andriibessarab/skewbot/cad/Vex Parts/Robot Battery (Li-Ion) (228-7045).SLDPRT

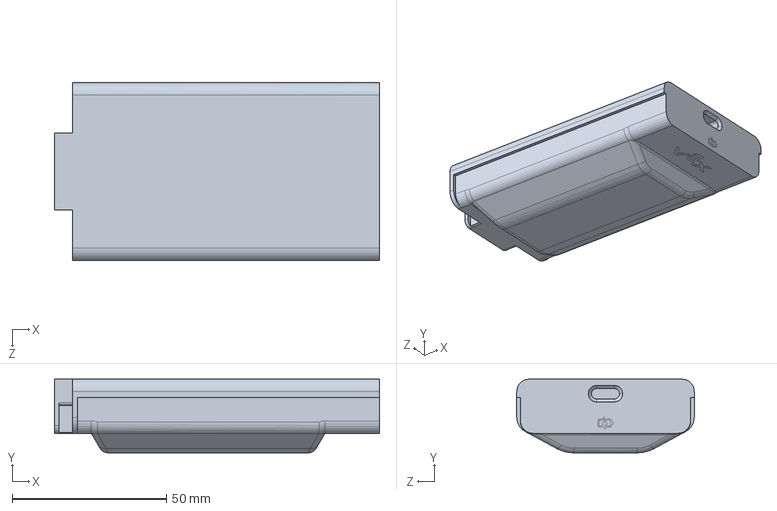
[picture p3: CAD file, 2025-11-20]
cad/Vex Parts/Robot Battery (Li-Ion) (228-7045).SLDPRT
105.5 x 23.9 x 57.6 mm
