andriibessarab/skewbot/cad/Vex Parts/2x Wide, 2x2 Corner Connector (228-2500-134).SLDPRT

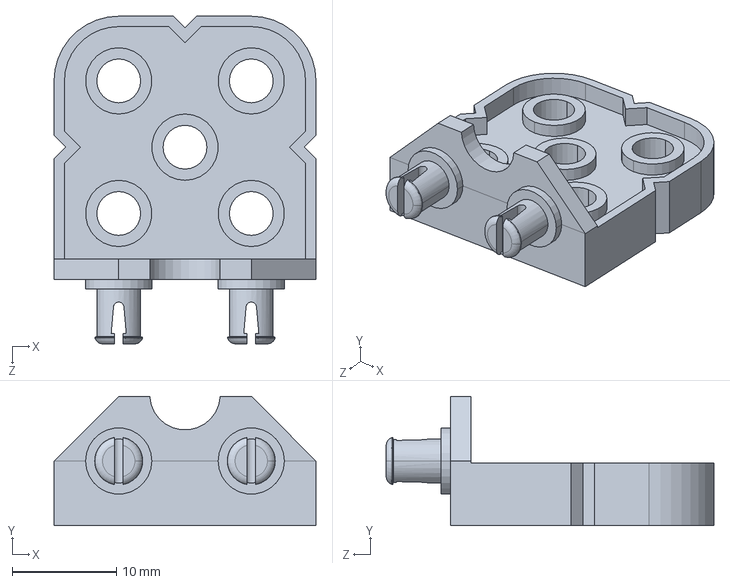
[picture p4: CAD file, 2025-11-20]
cad/Vex Parts/2x Wide, 2x2 Corner Connector (228-2500-134).SLDPRT
25.1 x 12.4 x 31.4 mm
