andriibessarab/skewbot/cad/Vex Parts/1x2 Connector Pin (228-2500-061).SLDPRT

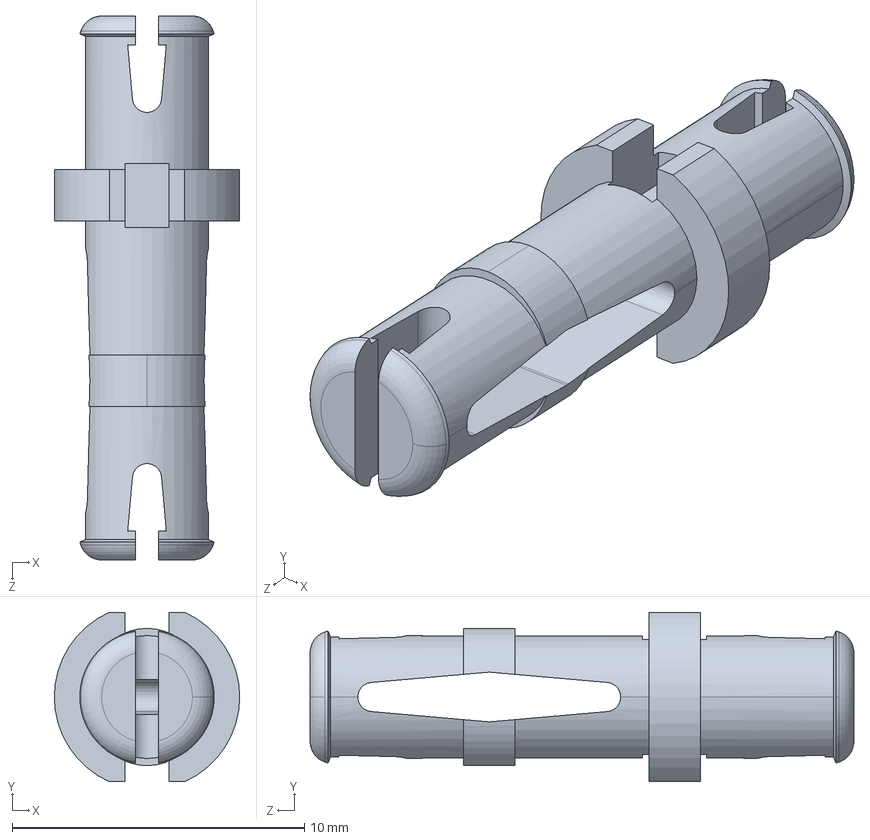
[picture p5: CAD file, 2025-11-20]
cad/Vex Parts/1x2 Connector Pin (228-2500-061).SLDPRT
6.35 x 5.80 x 18.6 mm
