andriibessarab/skewbot/cad/Vex Parts/VEX IQ Robot Brain Gen 2 (228-6480).SLDPRT

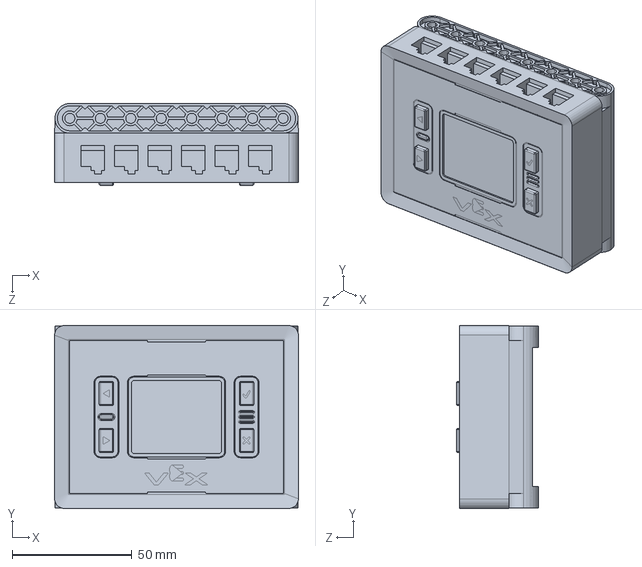
[picture p6: CAD file, 2025-11-20]
cad/Vex Parts/VEX IQ Robot Brain Gen 2 (228-6480).SLDPRT
101.7 x 76.3 x 34.2 mm
