andriibessarab/skewbot/cad/Vex Parts/1x4 Beam (228-2500-003).SLDPRT

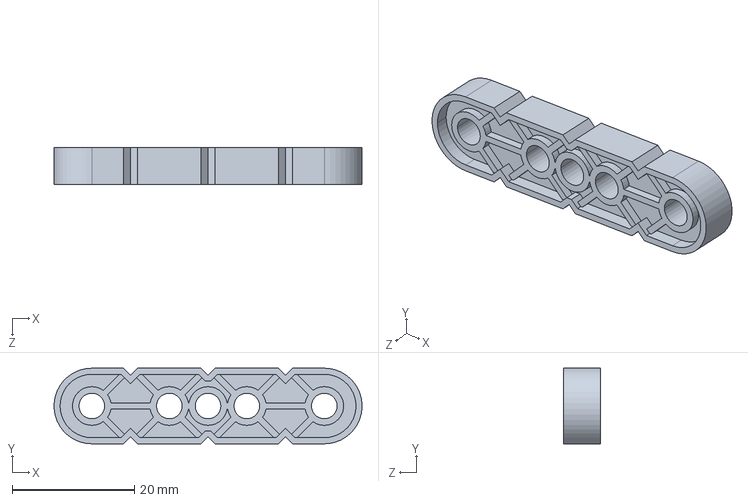
[picture p7: CAD file, 2025-11-20]
cad/Vex Parts/1x4 Beam (228-2500-003).SLDPRT
50.5 x 12.4 x 6.10 mm
