andriibessarab/skewbot/cad/Vex Parts/3x3 45 Degree Angle Beam (228-2500-148).SLDPRT

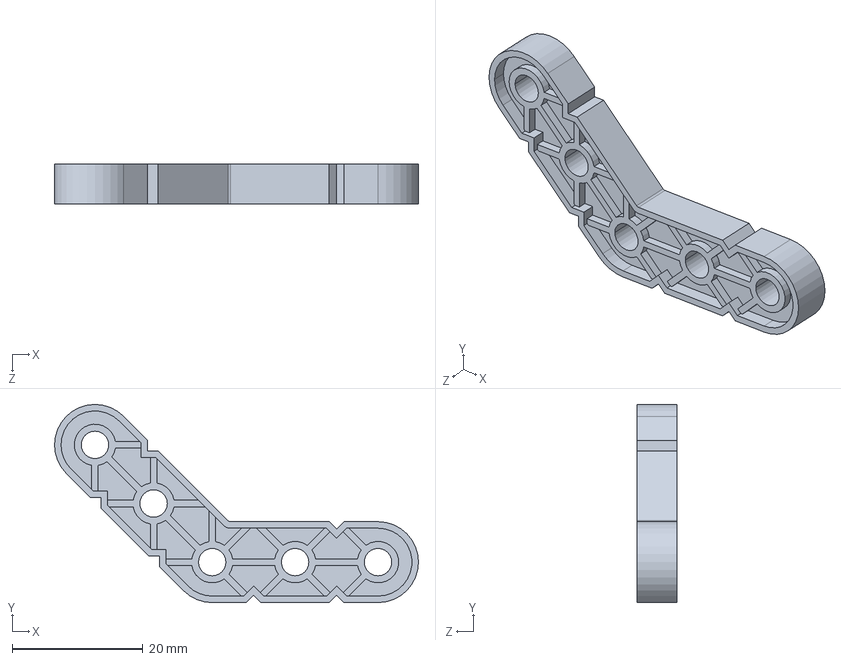
[picture p8: CAD file, 2025-11-20]
cad/Vex Parts/3x3 45 Degree Angle Beam (228-2500-148).SLDPRT
55.8 x 30.4 x 6.10 mm
