andriibessarab/skewbot/cad/Parts/Mirror Motor Mount Left.SLDPRT

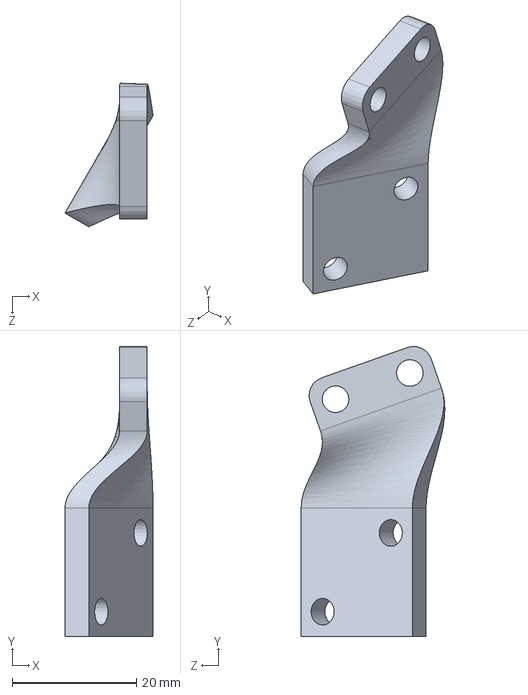
[picture p9: CAD file, 2025-11-20]
cad/Parts/Mirror Motor Mount Left.SLDPRT
14.2 x 46.8 x 23.2 mm
