andriibessarab/skewbot/cad/Vex Parts/1x3 Beam (228-2500-002).SLDPRT

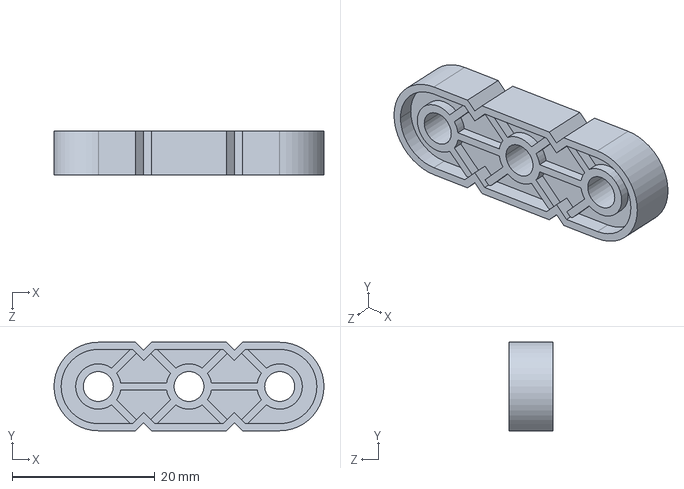
[picture p10: CAD file, 2025-11-20]
cad/Vex Parts/1x3 Beam (228-2500-002).SLDPRT
37.8 x 12.4 x 6.10 mm
