andriibessarab/skewbot/cad/Vex Parts/3x5 Right Angle Beam (228-2500-150).SLDPRT

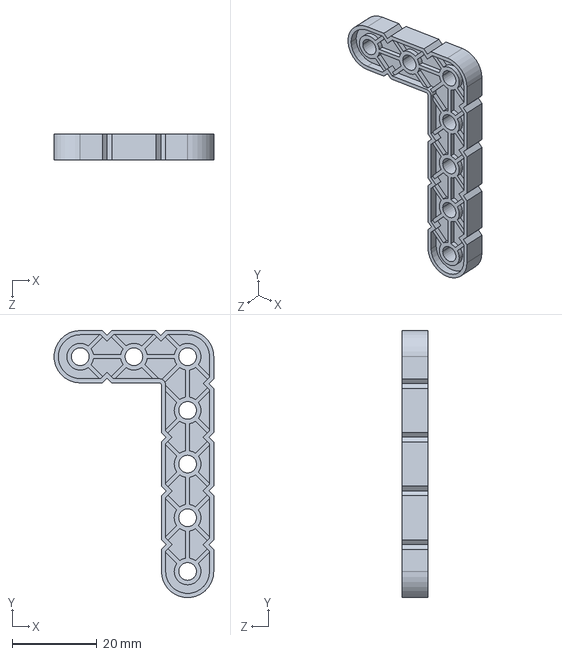
[picture p11: CAD file, 2025-11-20]
cad/Vex Parts/3x5 Right Angle Beam (228-2500-150).SLDPRT
37.8 x 63.2 x 6.10 mm
