andriibessarab/skewbot/cad/Parts/Top Back Brace.SLDPRT

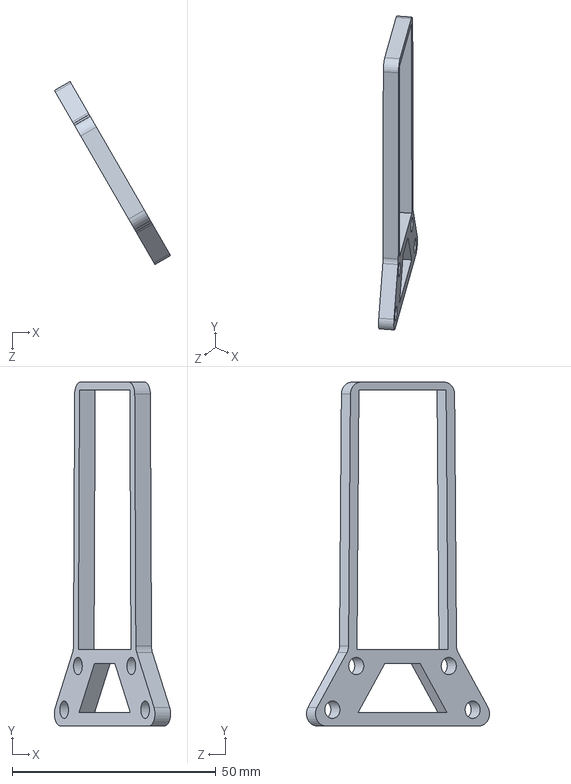
[picture p12: CAD file, 2025-11-20]
cad/Parts/Top Back Brace.SLDPRT
28.6 x 84.5 x 45.0 mm
