andriibessarab/skewbot/cad/Vex Parts/3x Motor Shaft.SLDPRT

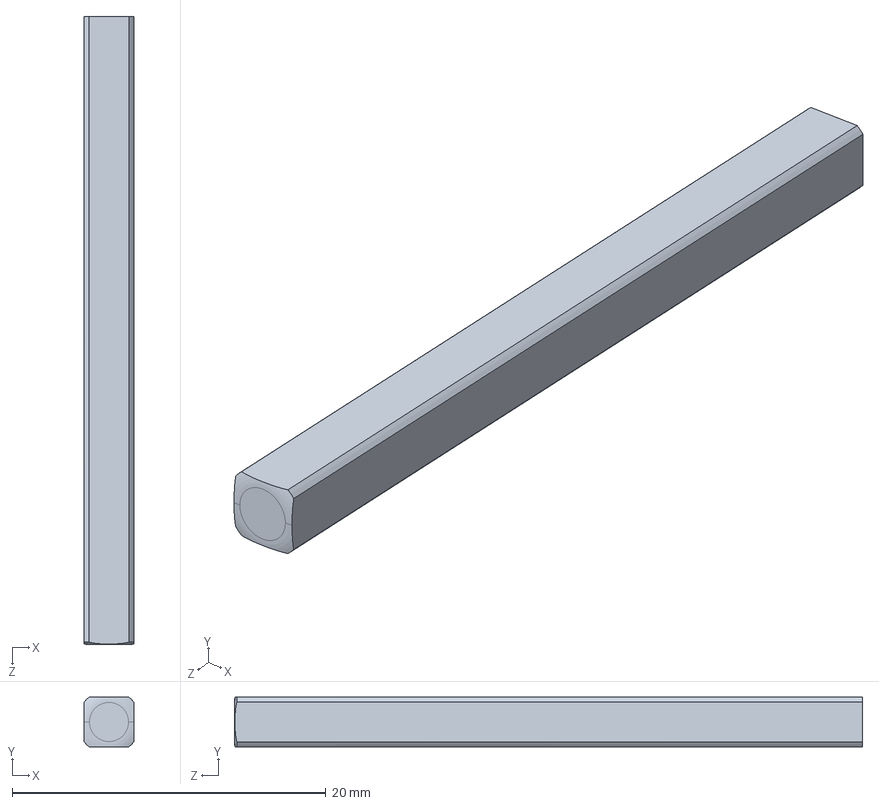
[picture p13: CAD file, 2025-11-20]
cad/Vex Parts/3x Motor Shaft.SLDPRT
3.17 x 3.17 x 40.0 mm
