andriibessarab/skewbot/cad/Vex Parts/VEX IQ Optical Sensor (228-7082).SLDPRT

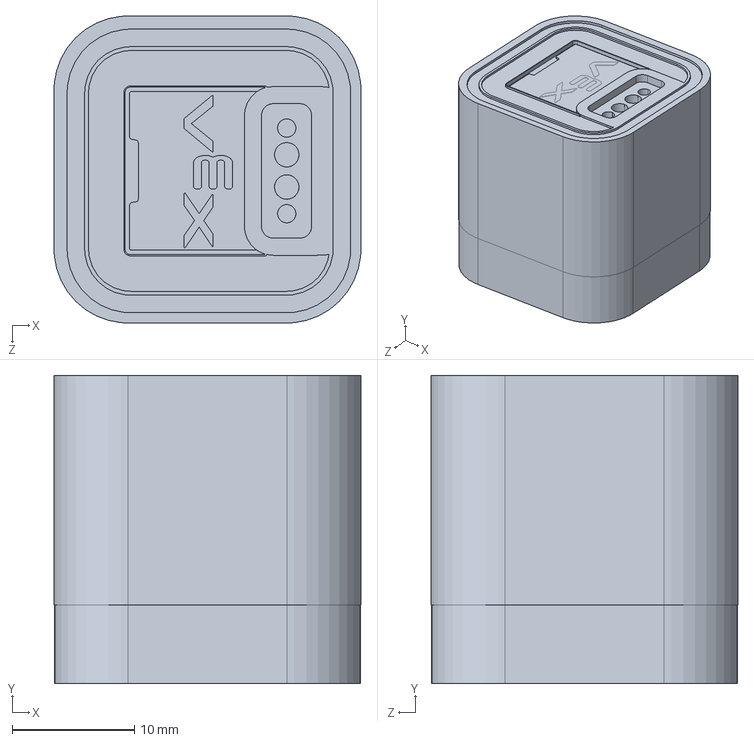
[picture p14: CAD file, 2025-11-20]
cad/Vex Parts/VEX IQ Optical Sensor (228-7082).SLDPRT
25.1 x 25.2 x 25.1 mm
