andriibessarab/skewbot/cad/Vex Parts/Double 2x Wide, 2x2 Double Offset Corner Connector (228-2500-277).SLDPRT

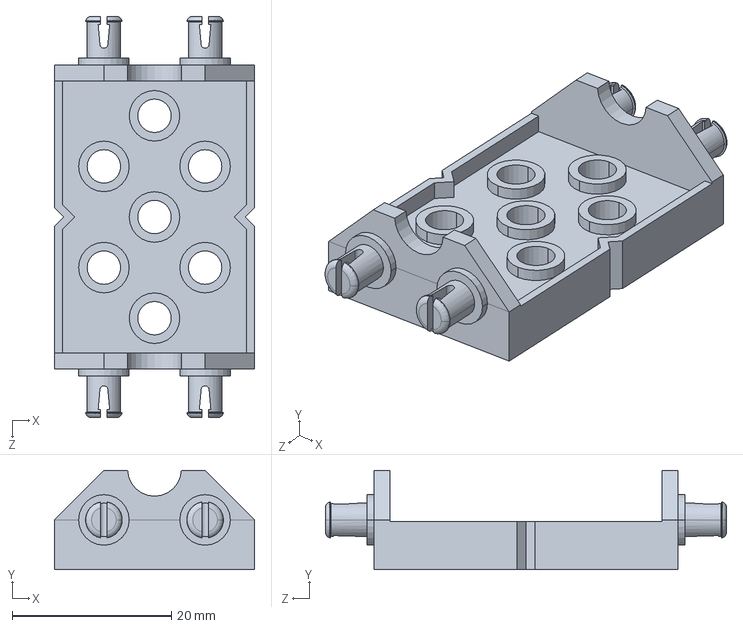
[picture p15: CAD file, 2025-11-20]
cad/Vex Parts/Double 2x Wide, 2x2 Double Offset Corner Connector (228-2500-277).SLDPRT
25.1 x 12.4 x 50.4 mm
