andriibessarab/skewbot/cad/Vex Parts/Triple 2x Wide, 2x2 Corner Connector (228-2500-1253).SLDPRT

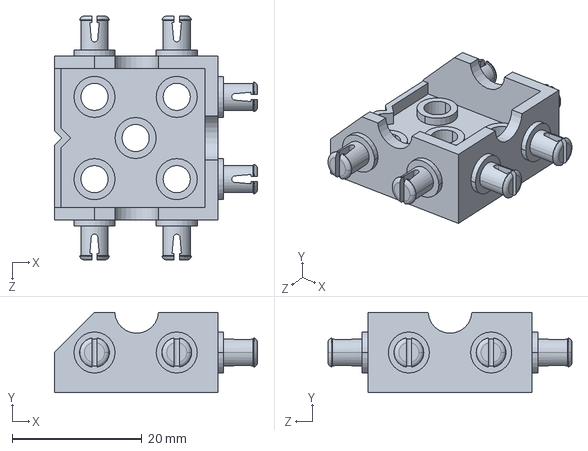
[picture p16: CAD file, 2025-11-20]
cad/Vex Parts/Triple 2x Wide, 2x2 Corner Connector (228-2500-1253).SLDPRT
31.4 x 12.4 x 37.7 mm
