andriibessarab/skewbot/cad/Vex Parts/1x2 Beam (228-2500-001).SLDPRT

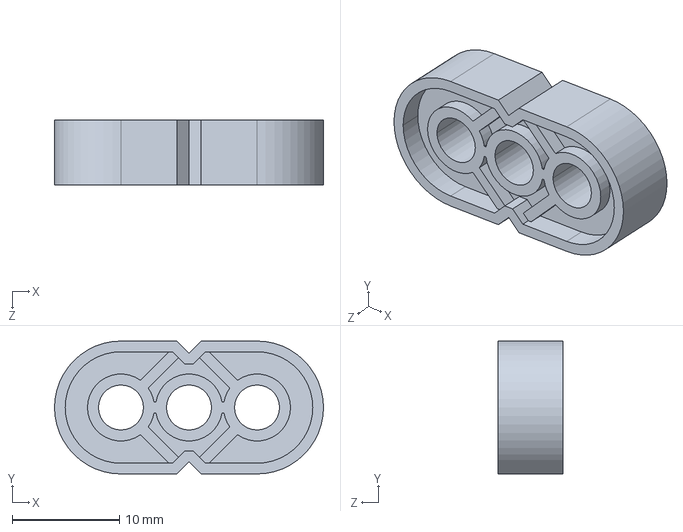
[picture p17: CAD file, 2025-11-20]
cad/Vex Parts/1x2 Beam (228-2500-001).SLDPRT
25.1 x 12.4 x 6.10 mm
