andriibessarab/skewbot/cad/Vex Parts/2x Wide, 1x2 Corner Connector (228-2500-128).SLDPRT

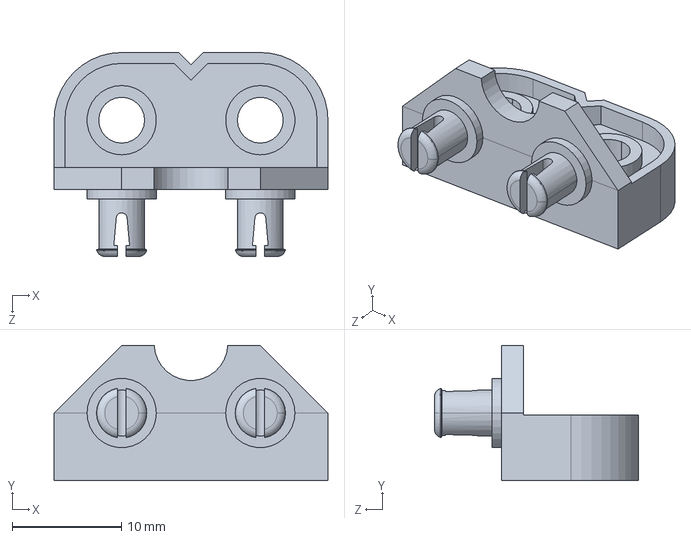
[picture p18: CAD file, 2025-11-20]
cad/Vex Parts/2x Wide, 1x2 Corner Connector (228-2500-128).SLDPRT
25.1 x 12.4 x 18.7 mm
