andriibessarab/skewbot/cad/Vex Parts/VEX IQ Touch LED (228-3010).SLDPRT

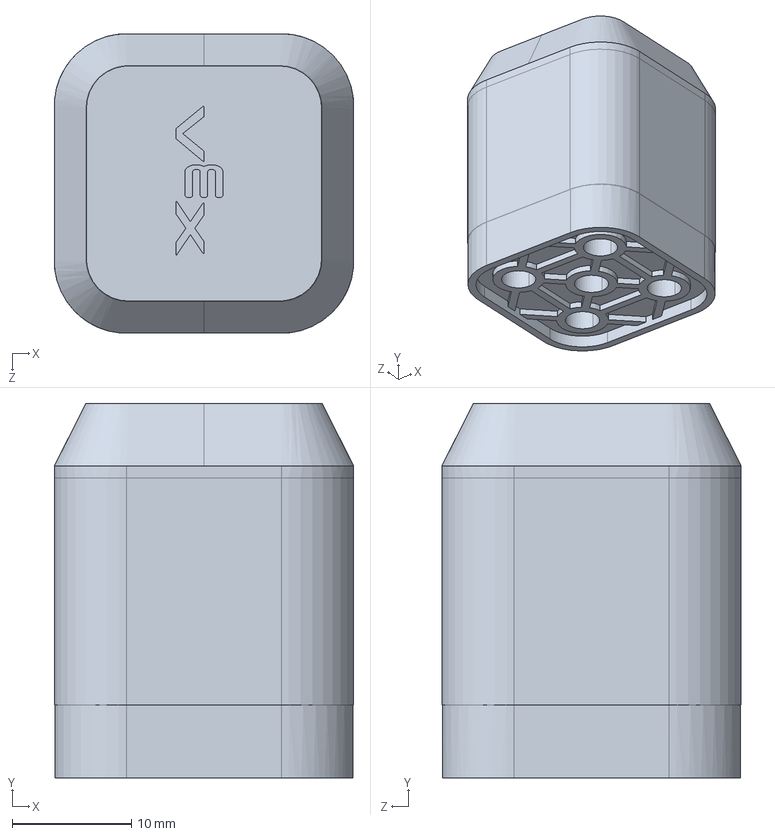
[picture p19: CAD file, 2025-11-20]
cad/Vex Parts/VEX IQ Touch LED (228-3010).SLDPRT
25.1 x 31.4 x 25.1 mm
