andriibessarab/skewbot/cad/Vex Parts/Small Chassis Corner Connector (228-2500-127).SLDPRT

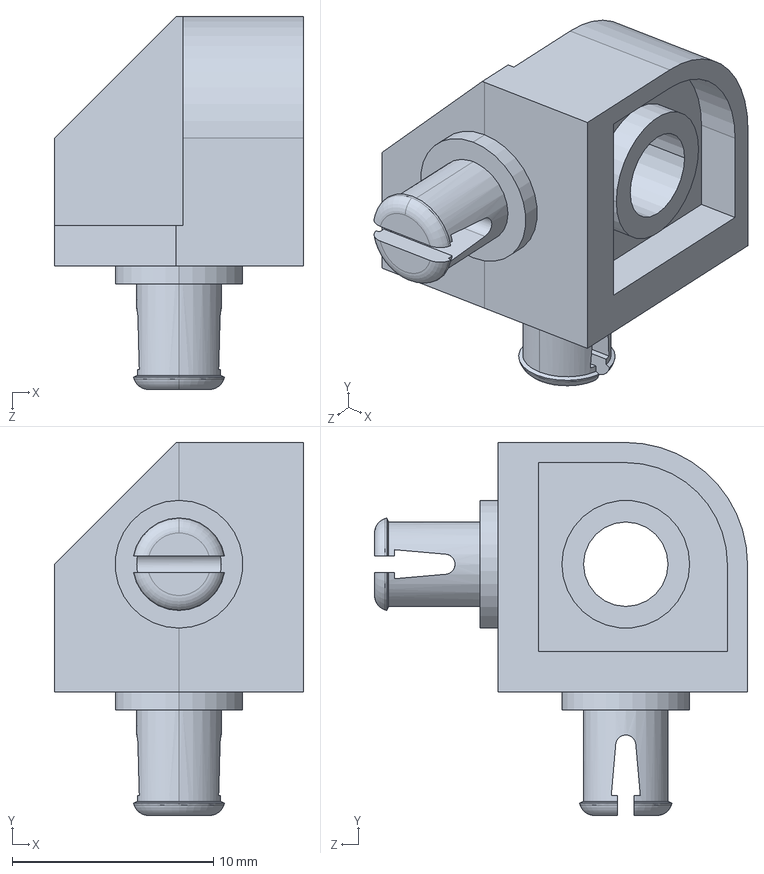
[picture p20: CAD file, 2025-11-20]
cad/Vex Parts/Small Chassis Corner Connector (228-2500-127).SLDPRT
12.4 x 18.5 x 18.5 mm
