andriibessarab/skewbot/vex-project/include/misc_functions.h

//----------------------------------------------------------------------------
//
//  Module:       misc_functions.h
//  Description:  Definitions & constants for misc. functions used in main
//  Authors:      MTE 100 & 121 Group 15
//
//----------------------------------------------------------------------------

#ifndef MISC_FUNCTIONS_H
#define MISC_FUNCTIONS_H

#pragma once

#include "vex.h"
#include "robot_config.h"

void print_status(std::string status);

#endif
