andriibessarab/skewbot/vex-project/include/vex.h

//----------------------------------------------------------------------------
//
//  Module:       vex.h
//  Description:  Header file with all imports used in project.
//  Authors:      MTE 100 & 121 Group 15
//
//----------------------------------------------------------------------------

#ifndef VEX_H_
#define VEX_H_

#include "iq2_cpp.h"

#include <stdint.h>
#include <stdio.h>
#include <stdlib.h>
#include <string.h>
#include <math.h>
#include <array>
#include <string>
#include <cstdio> 
#include <map>
#include <vector>
#include <cmath>
#include <unordered_map>
#include <algorithm>
#include <cstring>

#endif
